fedecarne/AnalogInputModule/Copy_of_Testing/images/fourier.png

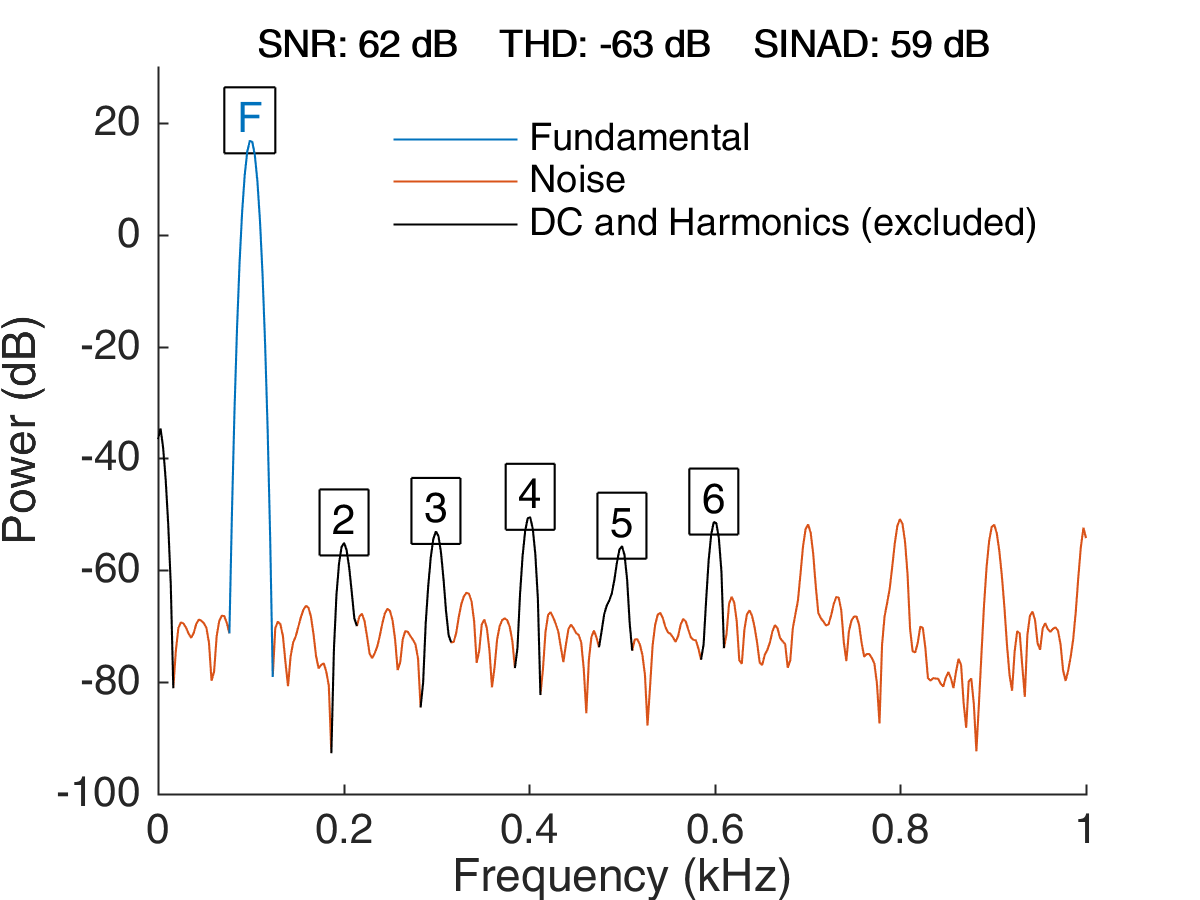
Copy_of_Testing/images/fourier.png
