fedecarne/AnalogInputModule/Testing/figs/fourier.png

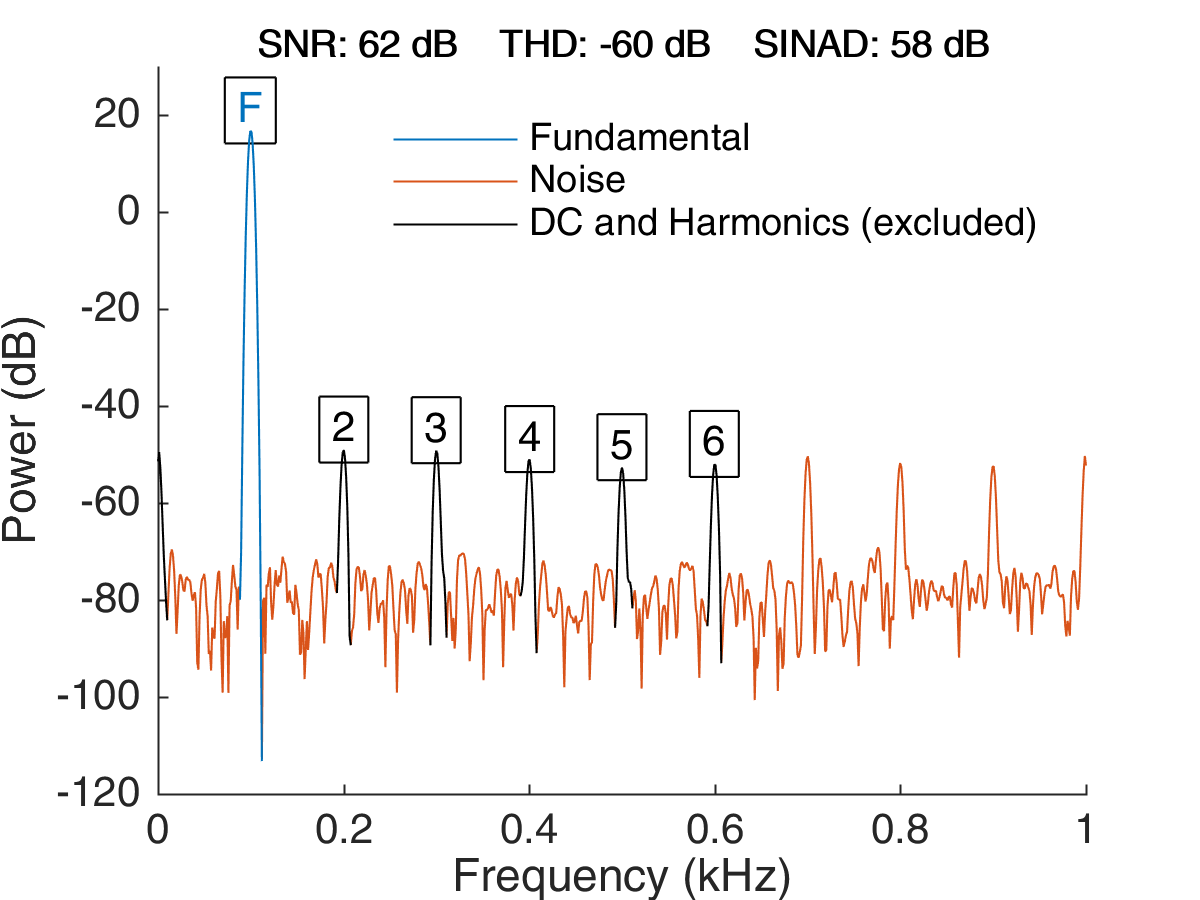
Testing/figs/fourier.png
