fedecarne/AnalogInputModule/Testing/figs/lite/fourier.png

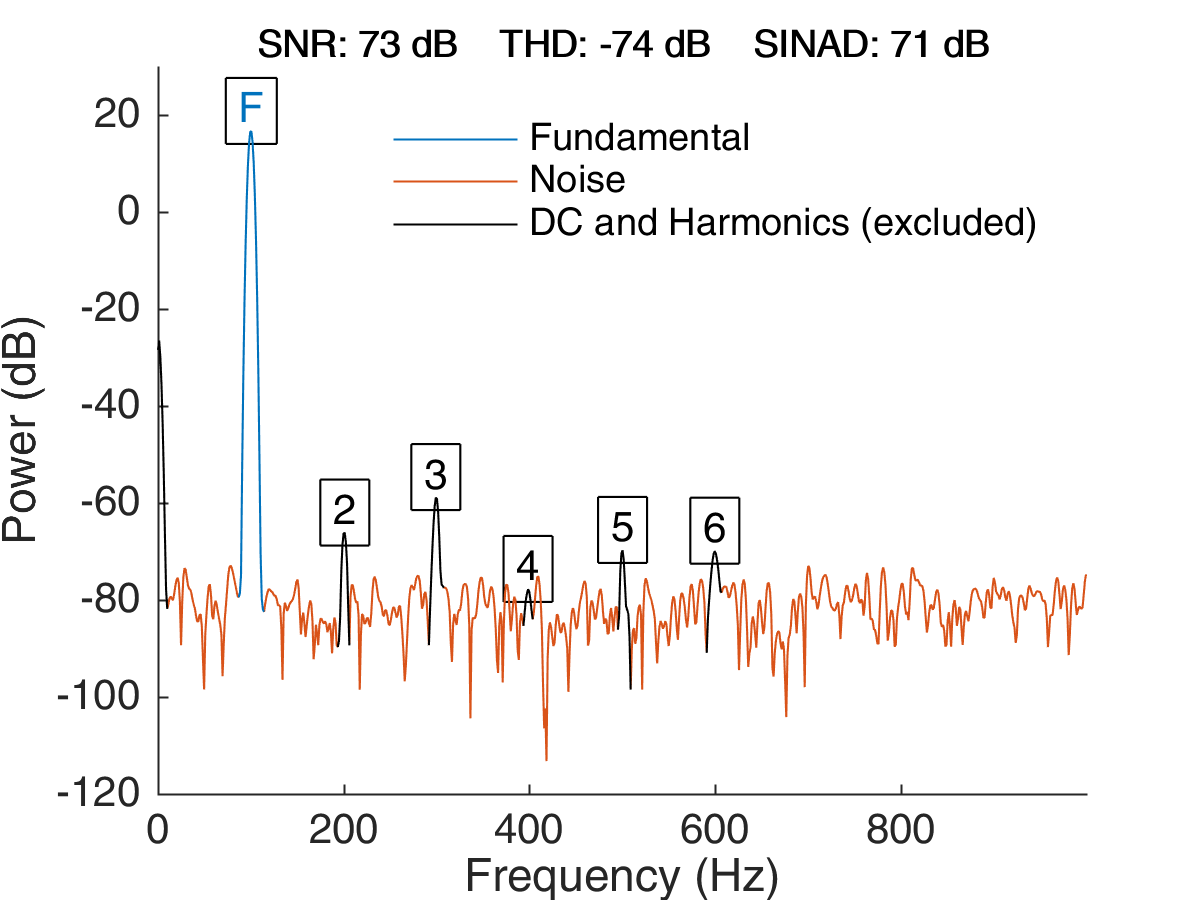
Testing/figs/lite/fourier.png
