fedecarne/AnalogInputModule/Testing/figs/lite/sine.png

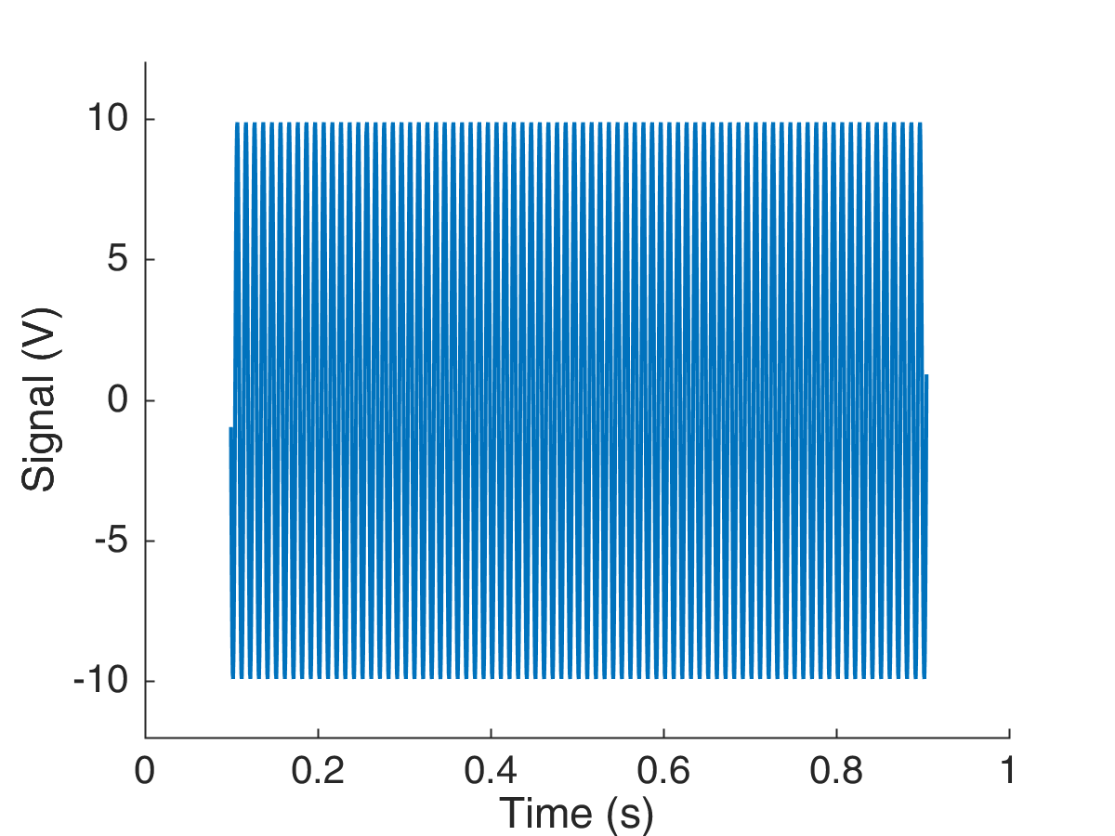
Testing/figs/lite/sine.png
