fedecarne/AnalogInputModule/Testing/figs/pro/fourier-pro.png

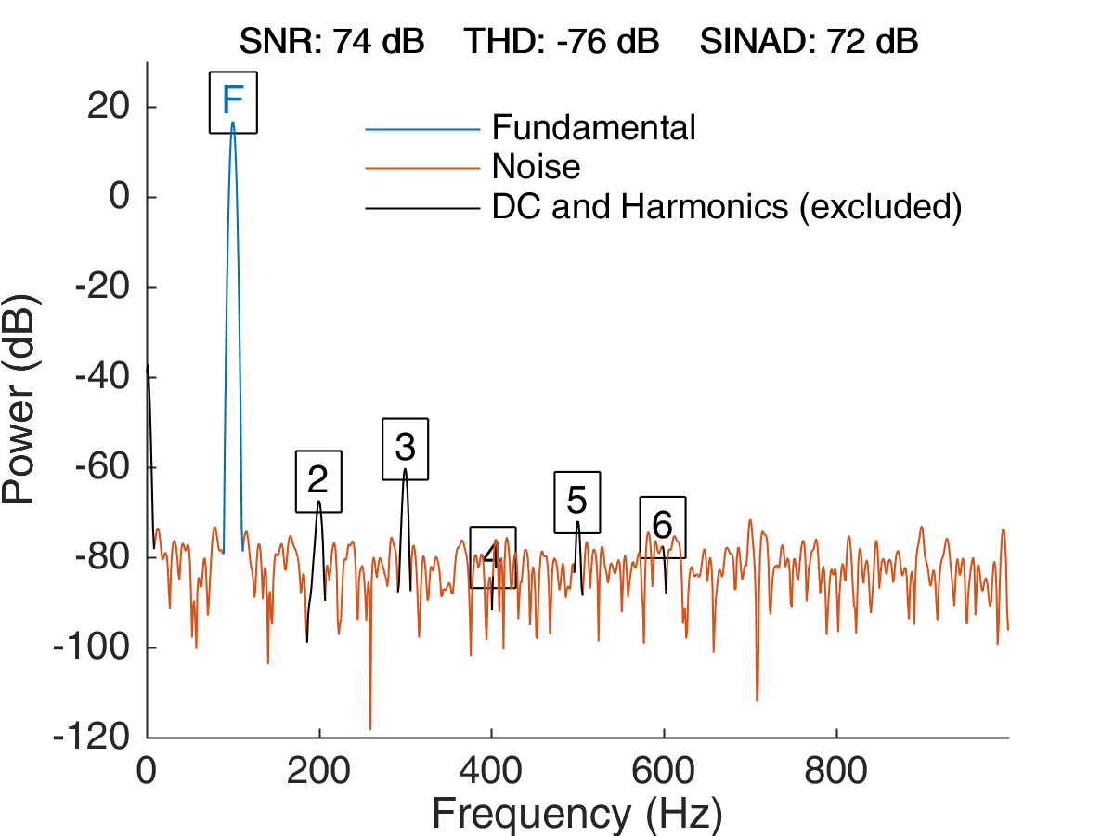
Testing/figs/pro/fourier-pro.png
