fedecarne/AnalogInputModule/Testing/figs/pro/sine.png

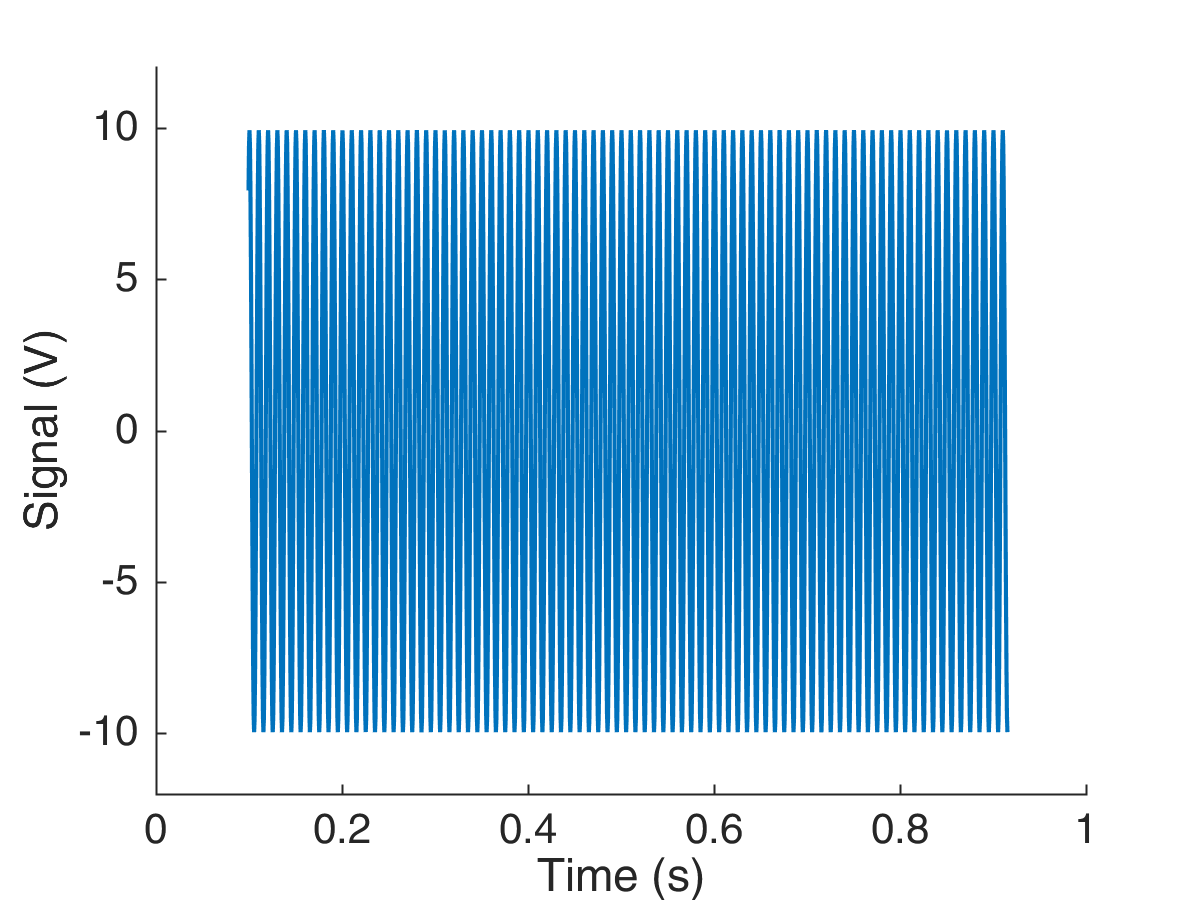
Testing/figs/pro/sine.png
