fedecarne/AnalogInputModule/Testing/figs/pro/SnrVsFs.png

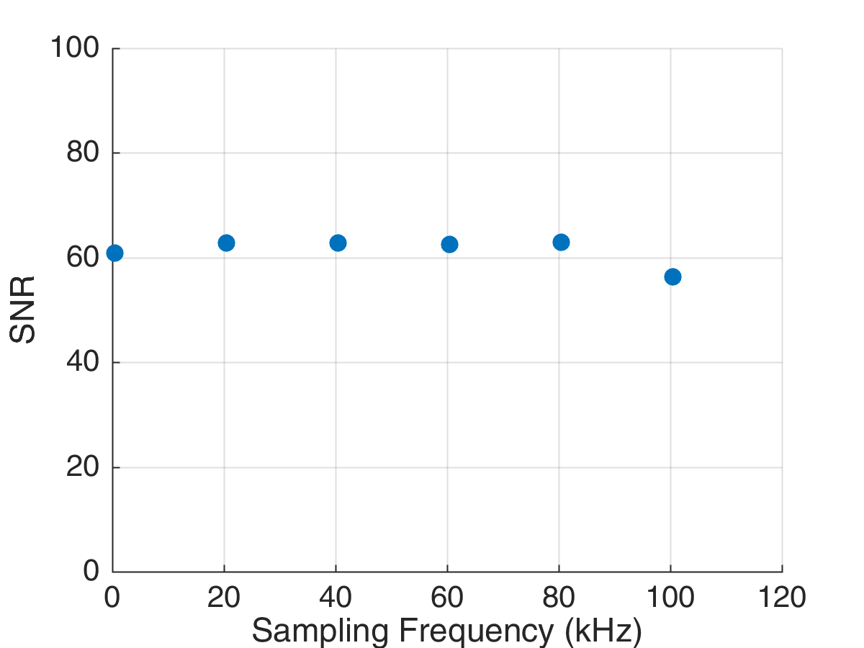
Testing/figs/pro/SnrVsFs.png
