fedecarne/AnalogInputModule/Testing/sine.png

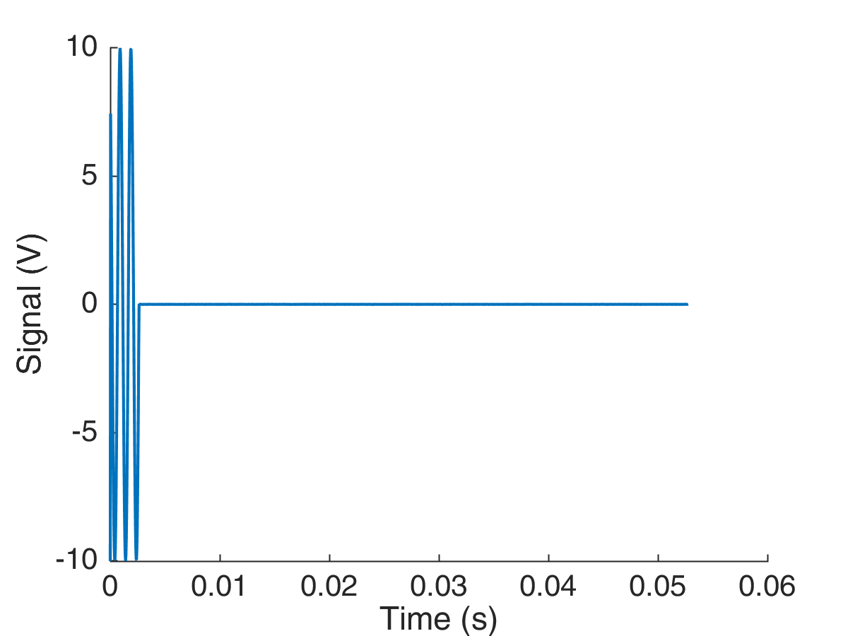
Testing/sine.png
